openamd/badge_firmware/firmware/opendopple/src/openbeacon.h

/***************************************************************
 *
 * OpenBeacon.org - OnAir protocol specification and definition
 *
 * Copyright 2006 Milosch Meriac <meriac@openbeacon.de>
 *
 ***************************************************************/

/*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
    You should have received a copy of the GNU General Public License along
    with this program; if not, write to the Free Software Foundation, Inc.,
    51 Franklin Street, Fifth Floor, Boston, MA 02110-1301 USA.

*/

#ifndef __OPENBEACON_H__
#define __OPENBEACON_H__

#define TEA_ENCRYPTION_BLOCK_COUNT 4

#define RFB_RFOPTIONS		0x0F

#define RFBPROTO_BEACONTRACKER	23
#define RFBPROTO_BEACONNODE	24
#define RFBPROTO_BEACONVOTESTATS	25

#define RFBFLAGS_ACK		0x01
#define RFBFLAGS_SENSOR		0x02
#define RFBFLAGS_VOTE_MASK      0x1C
#define RFBFLAGS_REQUEST_VOTE_TRANSMISSION  0x20


//No need to typedef what's standard on msp430.
//#include <types.h>
#include <signal.h>
#include <io.h>
#include <iomacros.h>
#include <stdlib.h>

/* Defined by stdlib.h on MSP430
typedef unsigned char u_int8_t;
typedef unsigned short u_int16_t;
typedef unsigned long u_int32_t;
*/


/*
 
 SZ PR FL ST SEQUENCENUM SOURCEIDXXX RESVD CRC16
 10 17 00 ff 00 0a 6f a7 ff ff ff ff 00 00 e7 53
 10 17 00 ff 00 0a 6f ab ff ff ff ff 00 00 b5 38
 10 17 00 aa 00 0a 6f ae ff ff ff ff 00 00 54 79
 10 17 00 ff 00 0a 6f b3 ff ff ff ff 00 00 11 ee
 10 17 00 ff 00 0a 6f b7 ff ff ff ff 00 00 d0 28
 10 17 00 aa 00 0a 6f ba ff ff ff ff 00 00 a2 c4

*/

typedef struct{
  u_int8_t size, proto;
} TBeaconHeader;

typedef struct{
  TBeaconHeader hdr;
  u_int8_t flags, strength;
  u_int32_t seq;
  u_int32_t oid;
  u_int16_t reserved;
  u_int16_t crc;
} TBeaconTracker;

typedef union{
  TBeaconTracker pkt;
  u_int32_t data[TEA_ENCRYPTION_BLOCK_COUNT];
  u_int8_t datab[TEA_ENCRYPTION_BLOCK_COUNT * sizeof (u_int32_t)];
}
TBeaconEnvelope;

#endif/*__OPENBEACON_H__*/
